bjornhij/freeDSP-aurora/ADDONS/AddOnA 1.0.0/KICAD/AddOnA.png

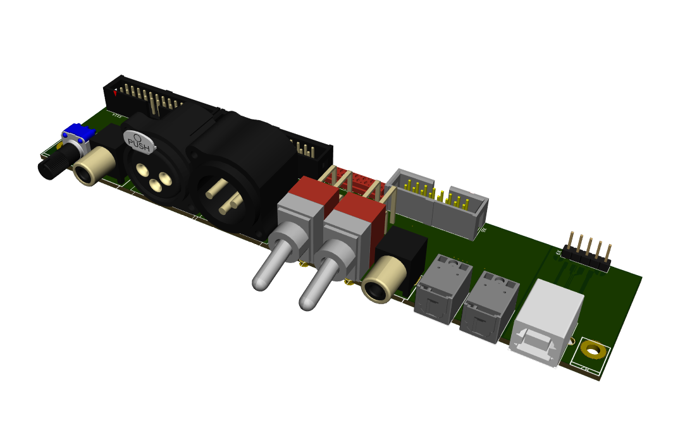
ADDONS/AddOnA 1.0.0/KICAD/AddOnA.png
