bjornhij/freeDSP-aurora/SOURCES/SIGMASTUDIO/HomeCinema71/HomeCinema71_IC_1_PARAM.h

/*
 * File:           Z:\Documents\freeDSP\freeDSP-aurora\SOURCES\SIGMASTUDIO\HomeCinema71\HomeCinema71_IC_1_PARAM.h
 *
 * Created:        Thursday, August 13, 2020 4:35:47 PM
 * Description:    HomeCinema71:IC 1 parameter RAM definitions.
 *
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
 * This software may only be used to program products purchased from
 * Analog Devices for incorporation by you into audio products that
 * are intended for resale to audio product end users. This software
 * may not be distributed whole or in any part to third parties.
 *
 * Copyright ©2020 Analog Devices, Inc. All rights reserved.
 */
#ifndef __HOMECINEMA71_IC_1_PARAM_H__
#define __HOMECINEMA71_IC_1_PARAM_H__


/* Module SafeLoadModule - SafeLoadModule*/
#define MOD_SAFELOADMODULE_COUNT                       7
#define MOD_SAFELOADMODULE_DEVICE                      "IC1"
#define MOD_SAFELOADMODULE_DATA_SAFELOAD0_ADDR         18832
#define MOD_SAFELOADMODULE_DATA_SAFELOAD1_ADDR         18833
#define MOD_SAFELOADMODULE_DATA_SAFELOAD2_ADDR         18834
#define MOD_SAFELOADMODULE_DATA_SAFELOAD3_ADDR         18835
#define MOD_SAFELOADMODULE_DATA_SAFELOAD4_ADDR         18836
#define MOD_SAFELOADMODULE_ADDRESS_SAFELOAD_ADDR       18837
#define MOD_SAFELOADMODULE_NUM_SAFELOAD_ADDR           18838

/* Module Shift1 - Arithmetic Shift*/
#define MOD_SHIFT1_COUNT                               1
#define MOD_SHIFT1_DEVICE                              "IC1"
#define MOD_SHIFT1_BITSHIFTADAU145XALG1SHIFTBITS_ADDR  18839
#define MOD_SHIFT1_BITSHIFTADAU145XALG1SHIFTBITS_FIXPT 0x0000000E
#define MOD_SHIFT1_BITSHIFTADAU145XALG1SHIFTBITS_VALUE SIGMASTUDIOTYPE_INTEGER_CONVERT(14)
#define MOD_SHIFT1_BITSHIFTADAU145XALG1SHIFTBITS_TYPE  SIGMASTUDIOTYPE_INTEGER

/* Module Low Shelv 1 - General Eq (2nd order)*/
#define MOD_LOWSHELV1_COUNT                            5
#define MOD_LOWSHELV1_DEVICE                           "IC1"
#define MOD_LOWSHELV1_ALG0_STAGE0_B2_ADDR              19200
#define MOD_LOWSHELV1_ALG0_STAGE0_B2_VALUE             SIGMASTUDIOTYPE_8_24_CONVERT(0.981658282617134)
#define MOD_LOWSHELV1_ALG0_STAGE0_B2_TYPE              SIGMASTUDIOTYPE_8_24
#define MOD_LOWSHELV1_ALG0_STAGE0_B1_ADDR              19201
#define MOD_LOWSHELV1_ALG0_STAGE0_B1_VALUE             SIGMASTUDIOTYPE_8_24_CONVERT(-1.98148850914457)
#define MOD_LOWSHELV1_ALG0_STAGE0_B1_TYPE              SIGMASTUDIOTYPE_8_24
#define MOD_LOWSHELV1_ALG0_STAGE0_B0_ADDR              19202
#define MOD_LOWSHELV1_ALG0_STAGE0_B0_VALUE             SIGMASTUDIOTYPE_8_24_CONVERT(1)
#define MOD_LOWSHELV1_ALG0_STAGE0_B0_TYPE              SIGMASTUDIOTYPE_8_24
#define MOD_LOWSHELV1_ALG0_STAGE0_A2_ADDR              19203
#define MOD_LOWSHELV1_ALG0_STAGE0_A2_VALUE             SIGMASTUDIOTYPE_8_24_CONVERT(-0.981658282617134)
#define MOD_LOWSHELV1_ALG0_STAGE0_A2_TYPE              SIGMASTUDIOTYPE_8_24
#define MOD_LOWSHELV1_ALG0_STAGE0_A1_ADDR              19204
#define MOD_LOWSHELV1_ALG0_STAGE0_A1_VALUE             SIGMASTUDIOTYPE_8_24_CONVERT(1.98148850914457)
#define MOD_LOWSHELV1_ALG0_STAGE0_A1_TYPE              SIGMASTUDIOTYPE_8_24

/* Module Low Shelv 2 - General Eq (2nd order)*/
#define MOD_LOWSHELV2_COUNT                            5
#define MOD_LOWSHELV2_DEVICE                           "IC1"
#define MOD_LOWSHELV2_ALG0_STAGE0_B2_ADDR              19205
#define MOD_LOWSHELV2_ALG0_STAGE0_B2_VALUE             SIGMASTUDIOTYPE_8_24_CONVERT(0.981658282617134)
#define MOD_LOWSHELV2_ALG0_STAGE0_B2_TYPE              SIGMASTUDIOTYPE_8_24
#define MOD_LOWSHELV2_ALG0_STAGE0_B1_ADDR              19206
#define MOD_LOWSHELV2_ALG0_STAGE0_B1_VALUE             SIGMASTUDIOTYPE_8_24_CONVERT(-1.98148850914457)
#define MOD_LOWSHELV2_ALG0_STAGE0_B1_TYPE              SIGMASTUDIOTYPE_8_24
#define MOD_LOWSHELV2_ALG0_STAGE0_B0_ADDR              19207
#define MOD_LOWSHELV2_ALG0_STAGE0_B0_VALUE             SIGMASTUDIOTYPE_8_24_CONVERT(1)
#define MOD_LOWSHELV2_ALG0_STAGE0_B0_TYPE              SIGMASTUDIOTYPE_8_24
#define MOD_LOWSHELV2_ALG0_STAGE0_A2_ADDR              19208
#define MOD_LOWSHELV2_ALG0_STAGE0_A2_VALUE             SIGMASTUDIOTYPE_8_24_CONVERT(-0.981658282617134)
#define MOD_LOWSHELV2_ALG0_STAGE0_A2_TYPE              SIGMASTUDIOTYPE_8_24
#define MOD_LOWSHELV2_ALG0_STAGE0_A1_ADDR              19209
#define MOD_LOWSHELV2_ALG0_STAGE0_A1_VALUE             SIGMASTUDIOTYPE_8_24_CONVERT(1.98148850914457)
#define MOD_LOWSHELV2_ALG0_STAGE0_A1_TYPE              SIGMASTUDIOTYPE_8_24

/* Module Low Shelv 3 - General Eq (2nd order)*/
#define MOD_LOWSHELV3_COUNT                            5
#define MOD_LOWSHELV3_DEVICE                           "IC1"
#define MOD_LOWSHELV3_ALG0_STAGE0_B2_ADDR              19210
#define MOD_LOWSHELV3_ALG0_STAGE0_B2_VALUE             SIGMASTUDIOTYPE_8_24_CONVERT(0.981658282617134)
#define MOD_LOWSHELV3_ALG0_STAGE0_B2_TYPE              SIGMASTUDIOTYPE_8_24
#define MOD_LOWSHELV3_ALG0_STAGE0_B1_ADDR              19211
#define MOD_LOWSHELV3_ALG0_STAGE0_B1_VALUE             SIGMASTUDIOTYPE_8_24_CONVERT(-1.98148850914457)
#define MOD_LOWSHELV3_ALG0_STAGE0_B1_TYPE              SIGMASTUDIOTYPE_8_24
#define MOD_LOWSHELV3_ALG0_STAGE0_B0_ADDR              19212
#define MOD_LOWSHELV3_ALG0_STAGE0_B0_VALUE             SIGMASTUDIOTYPE_8_24_CONVERT(1)
#define MOD_LOWSHELV3_ALG0_STAGE0_B0_TYPE              SIGMASTUDIOTYPE_8_24
#define MOD_LOWSHELV3_ALG0_STAGE0_A2_ADDR              19213
#define MOD_LOWSHELV3_ALG0_STAGE0_A2_VALUE             SIGMASTUDIOTYPE_8_24_CONVERT(-0.981658282617134)
#define MOD_LOWSHELV3_ALG0_STAGE0_A2_TYPE              SIGMASTUDIOTYPE_8_24
#define MOD_LOWSHELV3_ALG0_STAGE0_A1_ADDR              19214
#define MOD_LOWSHELV3_ALG0_STAGE0_A1_VALUE             SIGMASTUDIOTYPE_8_24_CONVERT(1.98148850914457)
#define MOD_LOWSHELV3_ALG0_STAGE0_A1_TYPE              SIGMASTUDIOTYPE_8_24

/* Module Low Shelv 4 - General Eq (2nd order)*/
#define MOD_LOWSHELV4_COUNT                            5
#define MOD_LOWSHELV4_DEVICE                           "IC1"
#define MOD_LOWSHELV4_ALG0_STAGE0_B2_ADDR              19215
#define MOD_LOWSHELV4_ALG0_STAGE0_B2_VALUE             SIGMASTUDIOTYPE_8_24_CONVERT(0.981658282617134)
#define MOD_LOWSHELV4_ALG0_STAGE0_B2_TYPE              SIGMASTUDIOTYPE_8_24
#define MOD_LOWSHELV4_ALG0_STAGE0_B1_ADDR              19216
#define MOD_LOWSHELV4_ALG0_STAGE0_B1_VALUE             SIGMASTUDIOTYPE_8_24_CONVERT(-1.98148850914457)
#define MOD_LOWSHELV4_ALG0_STAGE0_B1_TYPE              SIGMASTUDIOTYPE_8_24
#define MOD_LOWSHELV4_ALG0_STAGE0_B0_ADDR              19217
#define MOD_LOWSHELV4_ALG0_STAGE0_B0_VALUE             SIGMASTUDIOTYPE_8_24_CONVERT(1)
#define MOD_LOWSHELV4_ALG0_STAGE0_B0_TYPE              SIGMASTUDIOTYPE_8_24
#define MOD_LOWSHELV4_ALG0_STAGE0_A2_ADDR              19218
#define MOD_LOWSHELV4_ALG0_STAGE0_A2_VALUE             SIGMASTUDIOTYPE_8_24_CONVERT(-0.981658282617134)
#define MOD_LOWSHELV4_ALG0_STAGE0_A2_TYPE              SIGMASTUDIOTYPE_8_24
#define MOD_LOWSHELV4_ALG0_STAGE0_A1_ADDR              19219
#define MOD_LOWSHELV4_ALG0_STAGE0_A1_VALUE             SIGMASTUDIOTYPE_8_24_CONVERT(1.98148850914457)
#define MOD_LOWSHELV4_ALG0_STAGE0_A1_TYPE              SIGMASTUDIOTYPE_8_24

/* Module Low Shelv 5 - General Eq (2nd order)*/
#define MOD_LOWSHELV5_COUNT                            5
#define MOD_LOWSHELV5_DEVICE                           "IC1"
#define MOD_LOWSHELV5_ALG0_STAGE0_B2_ADDR              19220
#define MOD_LOWSHELV5_ALG0_STAGE0_B2_VALUE             SIGMASTUDIOTYPE_8_24_CONVERT(0.981658282617134)
#define MOD_LOWSHELV5_ALG0_STAGE0_B2_TYPE              SIGMASTUDIOTYPE_8_24
#define MOD_LOWSHELV5_ALG0_STAGE0_B1_ADDR              19221
#define MOD_LOWSHELV5_ALG0_STAGE0_B1_VALUE             SIGMASTUDIOTYPE_8_24_CONVERT(-1.98148850914457)
#define MOD_LOWSHELV5_ALG0_STAGE0_B1_TYPE              SIGMASTUDIOTYPE_8_24
#define MOD_LOWSHELV5_ALG0_STAGE0_B0_ADDR              19222
#define MOD_LOWSHELV5_ALG0_STAGE0_B0_VALUE             SIGMASTUDIOTYPE_8_24_CONVERT(1)
#define MOD_LOWSHELV5_ALG0_STAGE0_B0_TYPE              SIGMASTUDIOTYPE_8_24
#define MOD_LOWSHELV5_ALG0_STAGE0_A2_ADDR              19223
#define MOD_LOWSHELV5_ALG0_STAGE0_A2_VALUE             SIGMASTUDIOTYPE_8_24_CONVERT(-0.981658282617134)
#define MOD_LOWSHELV5_ALG0_STAGE0_A2_TYPE              SIGMASTUDIOTYPE_8_24
#define MOD_LOWSHELV5_ALG0_STAGE0_A1_ADDR              19224
#define MOD_LOWSHELV5_ALG0_STAGE0_A1_VALUE             SIGMASTUDIOTYPE_8_24_CONVERT(1.98148850914457)
#define MOD_LOWSHELV5_ALG0_STAGE0_A1_TYPE              SIGMASTUDIOTYPE_8_24

/* Module Low Shelv 6 - General Eq (2nd order)*/
#define MOD_LOWSHELV6_COUNT                            5
#define MOD_LOWSHELV6_DEVICE                           "IC1"
#define MOD_LOWSHELV6_ALG0_STAGE0_B2_ADDR              19225
#define MOD_LOWSHELV6_ALG0_STAGE0_B2_VALUE             SIGMASTUDIOTYPE_8_24_CONVERT(0.981658282617134)
#define MOD_LOWSHELV6_ALG0_STAGE0_B2_TYPE              SIGMASTUDIOTYPE_8_24
#define MOD_LOWSHELV6_ALG0_STAGE0_B1_ADDR              19226
#define MOD_LOWSHELV6_ALG0_STAGE0_B1_VALUE             SIGMASTUDIOTYPE_8_24_CONVERT(-1.98148850914457)
#define MOD_LOWSHELV6_ALG0_STAGE0_B1_TYPE              SIGMASTUDIOTYPE_8_24
#define MOD_LOWSHELV6_ALG0_STAGE0_B0_ADDR              19227
#define MOD_LOWSHELV6_ALG0_STAGE0_B0_VALUE             SIGMASTUDIOTYPE_8_24_CONVERT(1)
#define MOD_LOWSHELV6_ALG0_STAGE0_B0_TYPE              SIGMASTUDIOTYPE_8_24
#define MOD_LOWSHELV6_ALG0_STAGE0_A2_ADDR              19228
#define MOD_LOWSHELV6_ALG0_STAGE0_A2_VALUE             SIGMASTUDIOTYPE_8_24_CONVERT(-0.981658282617134)
#define MOD_LOWSHELV6_ALG0_STAGE0_A2_TYPE              SIGMASTUDIOTYPE_8_24
#define MOD_LOWSHELV6_ALG0_STAGE0_A1_ADDR              19229
#define MOD_LOWSHELV6_ALG0_STAGE0_A1_VALUE             SIGMASTUDIOTYPE_8_24_CONVERT(1.98148850914457)
#define MOD_LOWSHELV6_ALG0_STAGE0_A1_TYPE              SIGMASTUDIOTYPE_8_24

/* Module Low Shelv 7 - General Eq (2nd order)*/
#define MOD_LOWSHELV7_COUNT                            5
#define MOD_LOWSHELV7_DEVICE                           "IC1"
#define MOD_LOWSHELV7_ALG0_STAGE0_B2_ADDR              19230
#define MOD_LOWSHELV7_ALG0_STAGE0_B2_VALUE             SIGMASTUDIOTYPE_8_24_CONVERT(0.981658282617134)
#define MOD_LOWSHELV7_ALG0_STAGE0_B2_TYPE              SIGMASTUDIOTYPE_8_24
#define MOD_LOWSHELV7_ALG0_STAGE0_B1_ADDR              19231
#define MOD_LOWSHELV7_ALG0_STAGE0_B1_VALUE             SIGMASTUDIOTYPE_8_24_CONVERT(-1.98148850914457)
#define MOD_LOWSHELV7_ALG0_STAGE0_B1_TYPE              SIGMASTUDIOTYPE_8_24
#define MOD_LOWSHELV7_ALG0_STAGE0_B0_ADDR              19232
#define MOD_LOWSHELV7_ALG0_STAGE0_B0_VALUE             SIGMASTUDIOTYPE_8_24_CONVERT(1)
#define MOD_LOWSHELV7_ALG0_STAGE0_B0_TYPE              SIGMASTUDIOTYPE_8_24
#define MOD_LOWSHELV7_ALG0_STAGE0_A2_ADDR              19233
#define MOD_LOWSHELV7_ALG0_STAGE0_A2_VALUE             SIGMASTUDIOTYPE_8_24_CONVERT(-0.981658282617134)
#define MOD_LOWSHELV7_ALG0_STAGE0_A2_TYPE              SIGMASTUDIOTYPE_8_24
#define MOD_LOWSHELV7_ALG0_STAGE0_A1_ADDR              19234
#define MOD_LOWSHELV7_ALG0_STAGE0_A1_VALUE             SIGMASTUDIOTYPE_8_24_CONVERT(1.98148850914457)
#define MOD_LOWSHELV7_ALG0_STAGE0_A1_TYPE              SIGMASTUDIOTYPE_8_24

/* Module Low Shelv 8 - General Eq (2nd order)*/
#define MOD_LOWSHELV8_COUNT                            5
#define MOD_LOWSHELV8_DEVICE                           "IC1"
#define MOD_LOWSHELV8_ALG0_STAGE0_B2_ADDR              19235
#define MOD_LOWSHELV8_ALG0_STAGE0_B2_VALUE             SIGMASTUDIOTYPE_8_24_CONVERT(0.981658282617134)
#define MOD_LOWSHELV8_ALG0_STAGE0_B2_TYPE              SIGMASTUDIOTYPE_8_24
#define MOD_LOWSHELV8_ALG0_STAGE0_B1_ADDR              19236
#define MOD_LOWSHELV8_ALG0_STAGE0_B1_VALUE             SIGMASTUDIOTYPE_8_24_CONVERT(-1.98148850914457)
#define MOD_LOWSHELV8_ALG0_STAGE0_B1_TYPE              SIGMASTUDIOTYPE_8_24
#define MOD_LOWSHELV8_ALG0_STAGE0_B0_ADDR              19237
#define MOD_LOWSHELV8_ALG0_STAGE0_B0_VALUE             SIGMASTUDIOTYPE_8_24_CONVERT(1)
#define MOD_LOWSHELV8_ALG0_STAGE0_B0_TYPE              SIGMASTUDIOTYPE_8_24
#define MOD_LOWSHELV8_ALG0_STAGE0_A2_ADDR              19238
#define MOD_LOWSHELV8_ALG0_STAGE0_A2_VALUE             SIGMASTUDIOTYPE_8_24_CONVERT(-0.981658282617134)
#define MOD_LOWSHELV8_ALG0_STAGE0_A2_TYPE              SIGMASTUDIOTYPE_8_24
#define MOD_LOWSHELV8_ALG0_STAGE0_A1_ADDR              19239
#define MOD_LOWSHELV8_ALG0_STAGE0_A1_VALUE             SIGMASTUDIOTYPE_8_24_CONVERT(1.98148850914457)
#define MOD_LOWSHELV8_ALG0_STAGE0_A1_TYPE              SIGMASTUDIOTYPE_8_24

/* Module Param EQ 1 - Parametric EQ*/
#define MOD_PARAMEQ1_COUNT                             50
#define MOD_PARAMEQ1_DEVICE                            "IC1"
#define MOD_PARAMEQ1_ALG0_STAGE0_B2_ADDR               19240
#define MOD_PARAMEQ1_ALG0_STAGE0_B2_VALUE              SIGMASTUDIOTYPE_8_24_CONVERT(0)
#define MOD_PARAMEQ1_ALG0_STAGE0_B2_TYPE               SIGMASTUDIOTYPE_8_24
#define MOD_PARAMEQ1_ALG0_STAGE0_B1_ADDR               19241
#define MOD_PARAMEQ1_ALG0_STAGE0_B1_VALUE              SIGMASTUDIOTYPE_8_24_CONVERT(0)
#define MOD_PARAMEQ1_ALG0_STAGE0_B1_TYPE               SIGMASTUDIOTYPE_8_24
#define MOD_PARAMEQ1_ALG0_STAGE0_B0_ADDR               19242
#define MOD_PARAMEQ1_ALG0_STAGE0_B0_VALUE              SIGMASTUDIOTYPE_8_24_CONVERT(1)
#define MOD_PARAMEQ1_ALG0_STAGE0_B0_TYPE               SIGMASTUDIOTYPE_8_24
#define MOD_PARAMEQ1_ALG0_STAGE0_A2_ADDR               19243
#define MOD_PARAMEQ1_ALG0_STAGE0_A2_VALUE              SIGMASTUDIOTYPE_8_24_CONVERT(0)
#define MOD_PARAMEQ1_ALG0_STAGE0_A2_TYPE               SIGMASTUDIOTYPE_8_24
#define MOD_PARAMEQ1_ALG0_STAGE0_A1_ADDR               19244
#define MOD_PARAMEQ1_ALG0_STAGE0_A1_VALUE              SIGMASTUDIOTYPE_8_24_CONVERT(0)
#define MOD_PARAMEQ1_ALG0_STAGE0_A1_TYPE               SIGMASTUDIOTYPE_8_24
#define MOD_PARAMEQ1_ALG0_STAGE1_B2_ADDR               19245
#define MOD_PARAMEQ1_ALG0_STAGE1_B2_VALUE              SIGMASTUDIOTYPE_8_24_CONVERT(0)
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
#define MOD_PARAMEQ8_ALG0_STAGE9_A1_ADDR               19639
#define MOD_PARAMEQ8_ALG0_STAGE9_A1_VALUE              SIGMASTUDIOTYPE_8_24_CONVERT(0)
#define MOD_PARAMEQ8_ALG0_STAGE9_A1_TYPE               SIGMASTUDIOTYPE_8_24

/* Module High Shelv 1 - General Eq (2nd order)*/
#define MOD_HIGHSHELV1_COUNT                           5
#define MOD_HIGHSHELV1_DEVICE                          "IC1"
#define MOD_HIGHSHELV1_ALG0_STAGE0_B2_ADDR             19640
#define MOD_HIGHSHELV1_ALG0_STAGE0_B2_VALUE            SIGMASTUDIOTYPE_8_24_CONVERT(0.188345160884045)
#define MOD_HIGHSHELV1_ALG0_STAGE0_B2_TYPE             SIGMASTUDIOTYPE_8_24
#define MOD_HIGHSHELV1_ALG0_STAGE0_B1_ADDR             19641
#define MOD_HIGHSHELV1_ALG0_STAGE0_B1_VALUE            SIGMASTUDIOTYPE_8_24_CONVERT(-0.30756635979221)
#define MOD_HIGHSHELV1_ALG0_STAGE0_B1_TYPE             SIGMASTUDIOTYPE_8_24
#define MOD_HIGHSHELV1_ALG0_STAGE0_B0_ADDR             19642
#define MOD_HIGHSHELV1_ALG0_STAGE0_B0_VALUE            SIGMASTUDIOTYPE_8_24_CONVERT(1)
#define MOD_HIGHSHELV1_ALG0_STAGE0_B0_TYPE             SIGMASTUDIOTYPE_8_24
#define MOD_HIGHSHELV1_ALG0_STAGE0_A2_ADDR             19643
#define MOD_HIGHSHELV1_ALG0_STAGE0_A2_VALUE            SIGMASTUDIOTYPE_8_24_CONVERT(-0.188345160884045)
#define MOD_HIGHSHELV1_ALG0_STAGE0_A2_TYPE             SIGMASTUDIOTYPE_8_24
#define MOD_HIGHSHELV1_ALG0_STAGE0_A1_ADDR             19644
#define MOD_HIGHSHELV1_ALG0_STAGE0_A1_VALUE            SIGMASTUDIOTYPE_8_24_CONVERT(0.30756635979221)
#define MOD_HIGHSHELV1_ALG0_STAGE0_A1_TYPE             SIGMASTUDIOTYPE_8_24

/* Module High Shelv 2 - General Eq (2nd order)*/
#define MOD_HIGHSHELV2_COUNT                           5
#define MOD_HIGHSHELV2_DEVICE                          "IC1"
#define MOD_HIGHSHELV2_ALG0_STAGE0_B2_ADDR             19645
#define MOD_HIGHSHELV2_ALG0_STAGE0_B2_VALUE            SIGMASTUDIOTYPE_8_24_CONVERT(0.188345160884045)
#define MOD_HIGHSHELV2_ALG0_STAGE0_B2_TYPE             SIGMASTUDIOTYPE_8_24
#define MOD_HIGHSHELV2_ALG0_STAGE0_B1_ADDR             19646
#define MOD_HIGHSHELV2_ALG0_STAGE0_B1_VALUE            SIGMASTUDIOTYPE_8_24_CONVERT(-0.30756635979221)
#define MOD_HIGHSHELV2_ALG0_STAGE0_B1_TYPE             SIGMASTUDIOTYPE_8_24
#define MOD_HIGHSHELV2_ALG0_STAGE0_B0_ADDR             19647
#define MOD_HIGHSHELV2_ALG0_STAGE0_B0_VALUE            SIGMASTUDIOTYPE_8_24_CONVERT(1)
#define MOD_HIGHSHELV2_ALG0_STAGE0_B0_TYPE             SIGMASTUDIOTYPE_8_24
#define MOD_HIGHSHELV2_ALG0_STAGE0_A2_ADDR             19648
#define MOD_HIGHSHELV2_ALG0_STAGE0_A2_VALUE            SIGMASTUDIOTYPE_8_24_CONVERT(-0.188345160884045)
#define MOD_HIGHSHELV2_ALG0_STAGE0_A2_TYPE             SIGMASTUDIOTYPE_8_24
#define MOD_HIGHSHELV2_ALG0_STAGE0_A1_ADDR             19649
#define MOD_HIGHSHELV2_ALG0_STAGE0_A1_VALUE            SIGMASTUDIOTYPE_8_24_CONVERT(0.30756635979221)
#define MOD_HIGHSHELV2_ALG0_STAGE0_A1_TYPE             SIGMASTUDIOTYPE_8_24

/* Module High Shelv 3 - General Eq (2nd order)*/
#define MOD_HIGHSHELV3_COUNT                           5
#define MOD_HIGHSHELV3_DEVICE                          "IC1"
#define MOD_HIGHSHELV3_ALG0_STAGE0_B2_ADDR             19650
#define MOD_HIGHSHELV3_ALG0_STAGE0_B2_VALUE            SIGMASTUDIOTYPE_8_24_CONVERT(0.188345160884045)
#define MOD_HIGHSHELV3_ALG0_STAGE0_B2_TYPE             SIGMASTUDIOTYPE_8_24
#define MOD_HIGHSHELV3_ALG0_STAGE0_B1_ADDR             19651
#define MOD_HIGHSHELV3_ALG0_STAGE0_B1_VALUE            SIGMASTUDIOTYPE_8_24_CONVERT(-0.30756635979221)
#define MOD_HIGHSHELV3_ALG0_STAGE0_B1_TYPE             SIGMASTUDIOTYPE_8_24
#define MOD_HIGHSHELV3_ALG0_STAGE0_B0_ADDR             19652
#define MOD_HIGHSHELV3_ALG0_STAGE0_B0_VALUE            SIGMASTUDIOTYPE_8_24_CONVERT(1)
#define MOD_HIGHSHELV3_ALG0_STAGE0_B0_TYPE             SIGMASTUDIOTYPE_8_24
#define MOD_HIGHSHELV3_ALG0_STAGE0_A2_ADDR             19653
#define MOD_HIGHSHELV3_ALG0_STAGE0_A2_VALUE            SIGMASTUDIOTYPE_8_24_CONVERT(-0.188345160884045)
#define MOD_HIGHSHELV3_ALG0_STAGE0_A2_TYPE             SIGMASTUDIOTYPE_8_24
#define MOD_HIGHSHELV3_ALG0_STAGE0_A1_ADDR             19654
#define MOD_HIGHSHELV3_ALG0_STAGE0_A1_VALUE            SIGMASTUDIOTYPE_8_24_CONVERT(0.30756635979221)
#define MOD_HIGHSHELV3_ALG0_STAGE0_A1_TYPE             SIGMASTUDIOTYPE_8_24

/* Module High Shelv 4 - General Eq (2nd order)*/
#define MOD_HIGHSHELV4_COUNT                           5
#define MOD_HIGHSHELV4_DEVICE                          "IC1"
#define MOD_HIGHSHELV4_ALG0_STAGE0_B2_ADDR             19655
#define MOD_HIGHSHELV4_ALG0_STAGE0_B2_VALUE            SIGMASTUDIOTYPE_8_24_CONVERT(0.188345160884045)
#define MOD_HIGHSHELV4_ALG0_STAGE0_B2_TYPE             SIGMASTUDIOTYPE_8_24
#define MOD_HIGHSHELV4_ALG0_STAGE0_B1_ADDR             19656
#define MOD_HIGHSHELV4_ALG0_STAGE0_B1_VALUE            SIGMASTUDIOTYPE_8_24_CONVERT(-0.30756635979221)
#define MOD_HIGHSHELV4_ALG0_STAGE0_B1_TYPE             SIGMASTUDIOTYPE_8_24
#define MOD_HIGHSHELV4_ALG0_STAGE0_B0_ADDR             19657
#define MOD_HIGHSHELV4_ALG0_STAGE0_B0_VALUE            SIGMASTUDIOTYPE_8_24_CONVERT(1)
#define MOD_HIGHSHELV4_ALG0_STAGE0_B0_TYPE             SIGMASTUDIOTYPE_8_24
#define MOD_HIGHSHELV4_ALG0_STAGE0_A2_ADDR             19658
#define MOD_HIGHSHELV4_ALG0_STAGE0_A2_VALUE            SIGMASTUDIOTYPE_8_24_CONVERT(-0.188345160884045)
#define MOD_HIGHSHELV4_ALG0_STAGE0_A2_TYPE             SIGMASTUDIOTYPE_8_24
#define MOD_HIGHSHELV4_ALG0_STAGE0_A1_ADDR             19659
#define MOD_HIGHSHELV4_ALG0_STAGE0_A1_VALUE            SIGMASTUDIOTYPE_8_24_CONVERT(0.30756635979221)
#define MOD_HIGHSHELV4_ALG0_STAGE0_A1_TYPE             SIGMASTUDIOTYPE_8_24

/* Module High Shelv 7 - General Eq (2nd order)*/
#define MOD_HIGHSHELV7_COUNT                           5
#define MOD_HIGHSHELV7_DEVICE                          "IC1"
#define MOD_HIGHSHELV7_ALG0_STAGE0_B2_ADDR             19660
#define MOD_HIGHSHELV7_ALG0_STAGE0_B2_VALUE            SIGMASTUDIOTYPE_8_24_CONVERT(0.188345160884045)
#define MOD_HIGHSHELV7_ALG0_STAGE0_B2_TYPE             SIGMASTUDIOTYPE_8_24
#define MOD_HIGHSHELV7_ALG0_STAGE0_B1_ADDR             19661
#define MOD_HIGHSHELV7_ALG0_STAGE0_B1_VALUE            SIGMASTUDIOTYPE_8_24_CONVERT(-0.30756635979221)
#define MOD_HIGHSHELV7_ALG0_STAGE0_B1_TYPE             SIGMASTUDIOTYPE_8_24
#define MOD_HIGHSHELV7_ALG0_STAGE0_B0_ADDR             19662
#define MOD_HIGHSHELV7_ALG0_STAGE0_B0_VALUE            SIGMASTUDIOTYPE_8_24_CONVERT(1)
#define MOD_HIGHSHELV7_ALG0_STAGE0_B0_TYPE             SIGMASTUDIOTYPE_8_24
#define MOD_HIGHSHELV7_ALG0_STAGE0_A2_ADDR             19663
#define MOD_HIGHSHELV7_ALG0_STAGE0_A2_VALUE            SIGMASTUDIOTYPE_8_24_CONVERT(-0.188345160884045)
#define MOD_HIGHSHELV7_ALG0_STAGE0_A2_TYPE             SIGMASTUDIOTYPE_8_24
#define MOD_HIGHSHELV7_ALG0_STAGE0_A1_ADDR             19664
#define MOD_HIGHSHELV7_ALG0_STAGE0_A1_VALUE            SIGMASTUDIOTYPE_8_24_CONVERT(0.30756635979221)
#define MOD_HIGHSHELV7_ALG0_STAGE0_A1_TYPE             SIGMASTUDIOTYPE_8_24

/* Module High Shelv 6 - General Eq (2nd order)*/
#define MOD_HIGHSHELV6_COUNT                           5
#define MOD_HIGHSHELV6_DEVICE                          "IC1"
#define MOD_HIGHSHELV6_ALG0_STAGE0_B2_ADDR             19665
#define MOD_HIGHSHELV6_ALG0_STAGE0_B2_VALUE            SIGMASTUDIOTYPE_8_24_CONVERT(0.188345160884045)
#define MOD_HIGHSHELV6_ALG0_STAGE0_B2_TYPE             SIGMASTUDIOTYPE_8_24
#define MOD_HIGHSHELV6_ALG0_STAGE0_B1_ADDR             19666
#define MOD_HIGHSHELV6_ALG0_STAGE0_B1_VALUE            SIGMASTUDIOTYPE_8_24_CONVERT(-0.30756635979221)
#define MOD_HIGHSHELV6_ALG0_STAGE0_B1_TYPE             SIGMASTUDIOTYPE_8_24
#define MOD_HIGHSHELV6_ALG0_STAGE0_B0_ADDR             19667
#define MOD_HIGHSHELV6_ALG0_STAGE0_B0_VALUE            SIGMASTUDIOTYPE_8_24_CONVERT(1)
#define MOD_HIGHSHELV6_ALG0_STAGE0_B0_TYPE             SIGMASTUDIOTYPE_8_24
#define MOD_HIGHSHELV6_ALG0_STAGE0_A2_ADDR             19668
#define MOD_HIGHSHELV6_ALG0_STAGE0_A2_VALUE            SIGMASTUDIOTYPE_8_24_CONVERT(-0.188345160884045)
#define MOD_HIGHSHELV6_ALG0_STAGE0_A2_TYPE             SIGMASTUDIOTYPE_8_24
#define MOD_HIGHSHELV6_ALG0_STAGE0_A1_ADDR             19669
#define MOD_HIGHSHELV6_ALG0_STAGE0_A1_VALUE            SIGMASTUDIOTYPE_8_24_CONVERT(0.30756635979221)
#define MOD_HIGHSHELV6_ALG0_STAGE0_A1_TYPE             SIGMASTUDIOTYPE_8_24

/* Module High Shelv 5 - General Eq (2nd order)*/
#define MOD_HIGHSHELV5_COUNT                           5
#define MOD_HIGHSHELV5_DEVICE                          "IC1"
#define MOD_HIGHSHELV5_ALG0_STAGE0_B2_ADDR             19670
#define MOD_HIGHSHELV5_ALG0_STAGE0_B2_VALUE            SIGMASTUDIOTYPE_8_24_CONVERT(0.188345160884045)
#define MOD_HIGHSHELV5_ALG0_STAGE0_B2_TYPE             SIGMASTUDIOTYPE_8_24
#define MOD_HIGHSHELV5_ALG0_STAGE0_B1_ADDR             19671
#define MOD_HIGHSHELV5_ALG0_STAGE0_B1_VALUE            SIGMASTUDIOTYPE_8_24_CONVERT(-0.30756635979221)
#define MOD_HIGHSHELV5_ALG0_STAGE0_B1_TYPE             SIGMASTUDIOTYPE_8_24
#define MOD_HIGHSHELV5_ALG0_STAGE0_B0_ADDR             19672
#define MOD_HIGHSHELV5_ALG0_STAGE0_B0_VALUE            SIGMASTUDIOTYPE_8_24_CONVERT(1)
#define MOD_HIGHSHELV5_ALG0_STAGE0_B0_TYPE             SIGMASTUDIOTYPE_8_24
#define MOD_HIGHSHELV5_ALG0_STAGE0_A2_ADDR             19673
#define MOD_HIGHSHELV5_ALG0_STAGE0_A2_VALUE            SIGMASTUDIOTYPE_8_24_CONVERT(-0.188345160884045)
#define MOD_HIGHSHELV5_ALG0_STAGE0_A2_TYPE             SIGMASTUDIOTYPE_8_24
#define MOD_HIGHSHELV5_ALG0_STAGE0_A1_ADDR             19674
#define MOD_HIGHSHELV5_ALG0_STAGE0_A1_VALUE            SIGMASTUDIOTYPE_8_24_CONVERT(0.30756635979221)
#define MOD_HIGHSHELV5_ALG0_STAGE0_A1_TYPE             SIGMASTUDIOTYPE_8_24

/* Module High Shelv 8 - General Eq (2nd order)*/
#define MOD_HIGHSHELV8_COUNT                           5
#define MOD_HIGHSHELV8_DEVICE                          "IC1"
#define MOD_HIGHSHELV8_ALG0_STAGE0_B2_ADDR             19675
#define MOD_HIGHSHELV8_ALG0_STAGE0_B2_VALUE            SIGMASTUDIOTYPE_8_24_CONVERT(0.188345160884045)
#define MOD_HIGHSHELV8_ALG0_STAGE0_B2_TYPE             SIGMASTUDIOTYPE_8_24
#define MOD_HIGHSHELV8_ALG0_STAGE0_B1_ADDR             19676
#define MOD_HIGHSHELV8_ALG0_STAGE0_B1_VALUE            SIGMASTUDIOTYPE_8_24_CONVERT(-0.30756635979221)
#define MOD_HIGHSHELV8_ALG0_STAGE0_B1_TYPE             SIGMASTUDIOTYPE_8_24
#define MOD_HIGHSHELV8_ALG0_STAGE0_B0_ADDR             19677
#define MOD_HIGHSHELV8_ALG0_STAGE0_B0_VALUE            SIGMASTUDIOTYPE_8_24_CONVERT(1)
#define MOD_HIGHSHELV8_ALG0_STAGE0_B0_TYPE             SIGMASTUDIOTYPE_8_24
#define MOD_HIGHSHELV8_ALG0_STAGE0_A2_ADDR             19678
#define MOD_HIGHSHELV8_ALG0_STAGE0_A2_VALUE            SIGMASTUDIOTYPE_8_24_CONVERT(-0.188345160884045)
#define MOD_HIGHSHELV8_ALG0_STAGE0_A2_TYPE             SIGMASTUDIOTYPE_8_24
#define MOD_HIGHSHELV8_ALG0_STAGE0_A1_ADDR             19679
#define MOD_HIGHSHELV8_ALG0_STAGE0_A1_VALUE            SIGMASTUDIOTYPE_8_24_CONVERT(0.30756635979221)
#define MOD_HIGHSHELV8_ALG0_STAGE0_A1_TYPE             SIGMASTUDIOTYPE_8_24

/* Module LP8_1 - General Eq (2nd order)*/
#define MOD_LP8_1_COUNT                                5
#define MOD_LP8_1_DEVICE                               "IC1"
#define MOD_LP8_1_ALG0_STAGE0_B2_ADDR                  19680
#define MOD_LP8_1_ALG0_STAGE0_B2_VALUE                 SIGMASTUDIOTYPE_8_24_CONVERT(0)
#define MOD_LP8_1_ALG0_STAGE0_B2_TYPE                  SIGMASTUDIOTYPE_8_24
#define MOD_LP8_1_ALG0_STAGE0_B1_ADDR                  19681
#define MOD_LP8_1_ALG0_STAGE0_B1_VALUE                 SIGMASTUDIOTYPE_8_24_CONVERT(0)
#define MOD_LP8_1_ALG0_STAGE0_B1_TYPE                  SIGMASTUDIOTYPE_8_24
#define MOD_LP8_1_ALG0_STAGE0_B0_ADDR                  19682
#define MOD_LP8_1_ALG0_STAGE0_B0_VALUE                 SIGMASTUDIOTYPE_8_24_CONVERT(1)
#define MOD_LP8_1_ALG0_STAGE0_B0_TYPE                  SIGMASTUDIOTYPE_8_24
#define MOD_LP8_1_ALG0_STAGE0_A2_ADDR                  19683
#define MOD_LP8_1_ALG0_STAGE0_A2_VALUE                 SIGMASTUDIOTYPE_8_24_CONVERT(0)
#define MOD_LP8_1_ALG0_STAGE0_A2_TYPE                  SIGMASTUDIOTYPE_8_24
#define MOD_LP8_1_ALG0_STAGE0_A1_ADDR                  19684
#define MOD_LP8_1_ALG0_STAGE0_A1_VALUE                 SIGMASTUDIOTYPE_8_24_CONVERT(0)
#define MOD_LP8_1_ALG0_STAGE0_A1_TYPE                  SIGMASTUDIOTYPE_8_24

/* Module LP8_2 - General Eq (2nd order)*/
#define MOD_LP8_2_COUNT                                5
#define MOD_LP8_2_DEVICE                               "IC1"
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
#define MOD_XO_HP2_1_ALG0_STAGE0_A1_ADDR               19699
#define MOD_XO_HP2_1_ALG0_STAGE0_A1_VALUE              SIGMASTUDIOTYPE_8_24_CONVERT(0)
#define MOD_XO_HP2_1_ALG0_STAGE0_A1_TYPE               SIGMASTUDIOTYPE_8_24
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
