bjornhij/freeDSP-aurora/SOURCES/WEBAPP/ESP32/aurora/plugin.cpp

#include <Arduino.h>
#include <ArduinoJson.h>
#include <SPIFFS.h>

#include "plugin.h"

tSettings Settings;

tInput paramInputs[8];
tHPLP paramHP[8];
tShelving paramLshelv[8];
tPeq paramPeq[80];
tShelving paramHshelv[8];
tHPLP paramLP[8];
tPhase paramPhase[8];
tDelay paramDelay[8];
tGain paramGain[8];
tCrossover paramCrossover[8];
tFir paramFir[MAX_NUM_FIRS];
tMasterVolume masterVolume = { 0x0000, -60.0 };
tInputSelector inputSelector;
tSpdifOutput spdifOutput;
tSpdifOutputSelector spdifOutputSelector;

int numInputs = 0;
int numHPs = 0;
int numLShelvs = 0;
int numPEQs = 0;
int numHShelvs = 0;
int numLPs = 0;
int numPhases = 0;
int numDelays = 0;
int numGains = 0;
int numCrossovers = 0;
int numFIRs = 0;

float sampleRate = 48000.0;

uint16_t addrVPot = 0x0000;

String currentPlugInName;

String presetUsrparamFile[MAX_NUM_PRESETS] = { "/usrparam.001", "/usrparam.002", "/usrparam.003", "/usrparam.004" };
String presetAddonCfgFile[MAX_NUM_PRESETS] = { "/addoncfg.001", "/addoncfg.002", "/addoncfg.003", "/addoncfg.004" };

uint8_t currentPreset = 0;

byte currentAddOnCfg[3];

float memIR[SIZE_IR_MEMORY];

//==============================================================================
/*! Reads the plugin meta data from JSON file.
 */
void readPluginMeta( void )
{
  Serial.print( "Reading plugin.ini......" );

  if( !SPIFFS.exists( "/plugin.ini" ) )
  {
    Serial.println( "File does not exist yet" );
    return;
  }

  File filePluginMeta = SPIFFS.open( "/plugin.ini" );

  if( filePluginMeta )
  {
    StaticJsonDocument<5000> jsonDoc;
    DeserializationError err = deserializeJson( jsonDoc, filePluginMeta );
    if( err )
    {
      Serial.print( "[ERROR] readPluginMeta(): Deserialization failed." );
      Serial.println( err.c_str() );
      return;
    }

    JsonObject jsonPluginMeta = jsonDoc.as<JsonObject>();

    currentPlugInName = jsonPluginMeta["name"].as<String>();
    numInputs = jsonPluginMeta["nchn"].as<String>().toInt();
    numHPs = jsonPluginMeta["nhp"].as<String>().toInt();
    numLShelvs = jsonPluginMeta["nlshelv"].as<String>().toInt();
    numPEQs = jsonPluginMeta["npeq"].as<String>().toInt();
    numHShelvs = jsonPluginMeta["nhshelv"].as<String>().toInt();
    numLPs = jsonPluginMeta["nlp"].as<String>().toInt();
    numPhases = jsonPluginMeta["nphase"].as<String>().toInt();
    numDelays = jsonPluginMeta["ndly"].as<String>().toInt();
    numGains = jsonPluginMeta["ngain"].as<String>().toInt();
    numCrossovers = jsonPluginMeta["nxo"].as<String>().toInt();
    numFIRs = jsonPluginMeta["nfir"].as<String>().toInt();

    for( int ii = 0; ii < numInputs; ii++ )
      inputSelector.analog[ii] = static_cast<uint16_t>(jsonPluginMeta["analog"][ii].as<String>().toInt());
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
